kiltum/usb-rs485/test/test/Inc/main.h

#define SPI_LATCH_Pin GPIO_PIN_4
#define SPI_LATCH_GPIO_Port GPIOA
#define SPI_DE_Pin GPIO_PIN_6
#define SPI_DE_GPIO_Port GPIOA
